loopj/periphlex/KiCad/periphlex.kicad_sch

## KiCad design KiCad/periphlex.kicad_sch (2024-03-02)

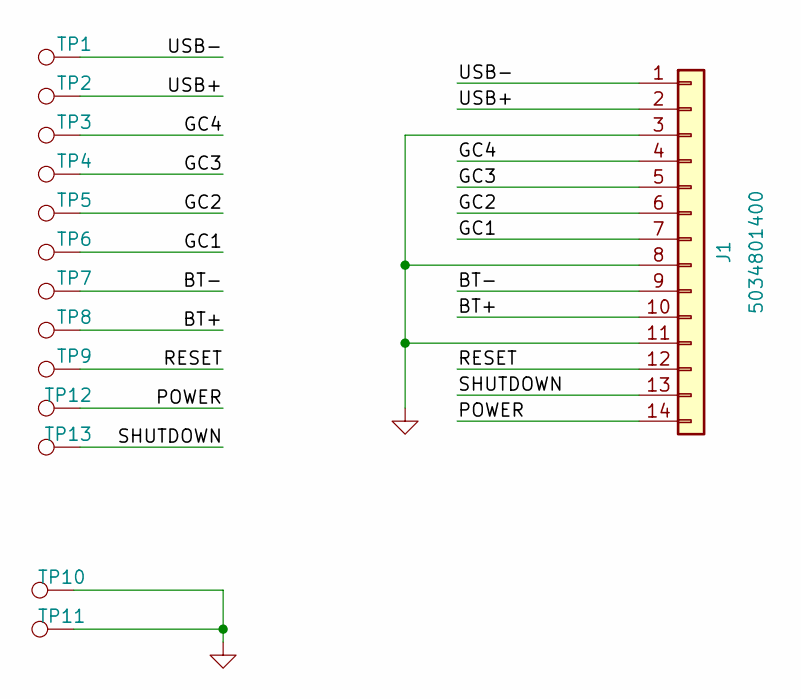
[picture p3: schematic periphlex.kicad_sch]

Parts:
J1: 5034801400
TP1, TP2, TP3, TP4, TP5, TP6, TP7, TP8, TP10, TP11, TP12: TestPoint; ViaPad_0.3_0.5
TP9, TP13: TestPoint; TestPoint_Pad_1.0x1.0mm

Connections:
BT+: J1.10, TP8.1
BT-: J1.9, TP7.1
GC1: J1.7, TP6.1
GC2: J1.6, TP5.1
GC3: J1.5, TP4.1
GC4: J1.4, TP3.1
GND: J1.3, J1.8, J1.11, TP10.1, TP11.1
POWER: J1.14, TP12.1
RESET: J1.12, TP9.1
SHUTDOWN: J1.13, TP13.1
USB+: J1.2, TP2.1
USB-: J1.1, TP1.1
